LiO2-coder/Smart-home-environment-monitoring-clock/images/2.png

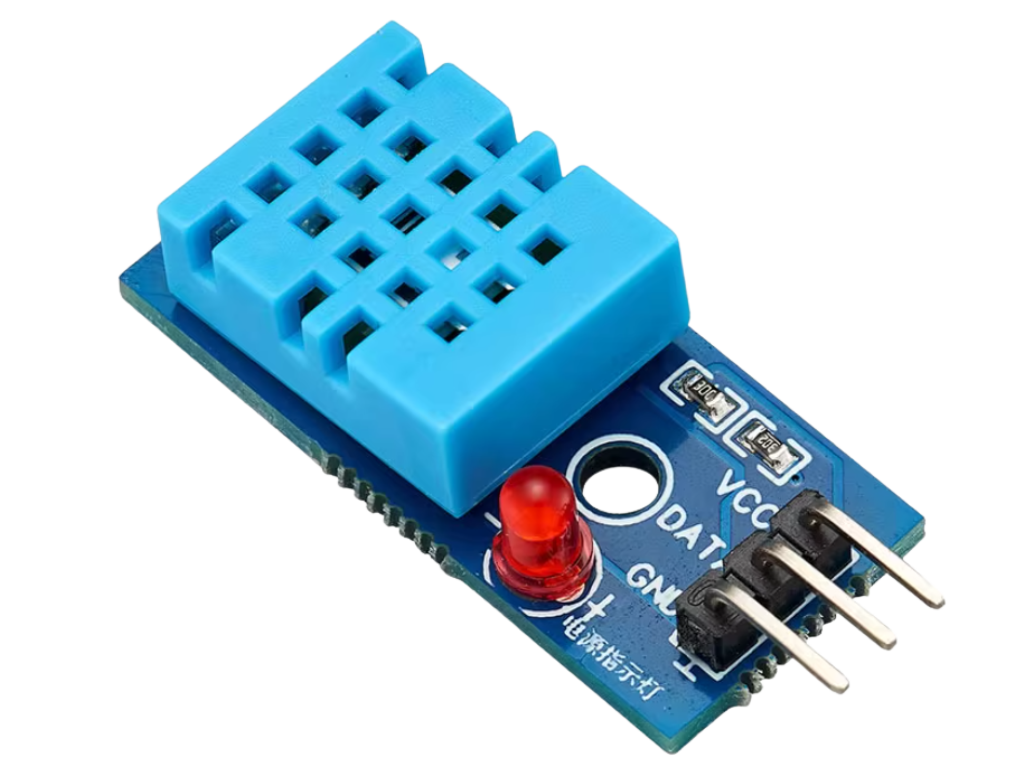
images/2.png
