LiO2-coder/Smart-home-environment-monitoring-clock/images/3.png

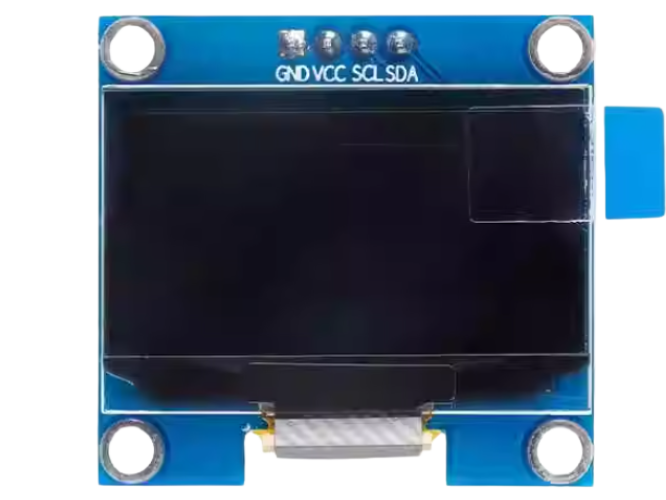
images/3.png
