LiO2-coder/Smart-home-environment-monitoring-clock/images/5.png

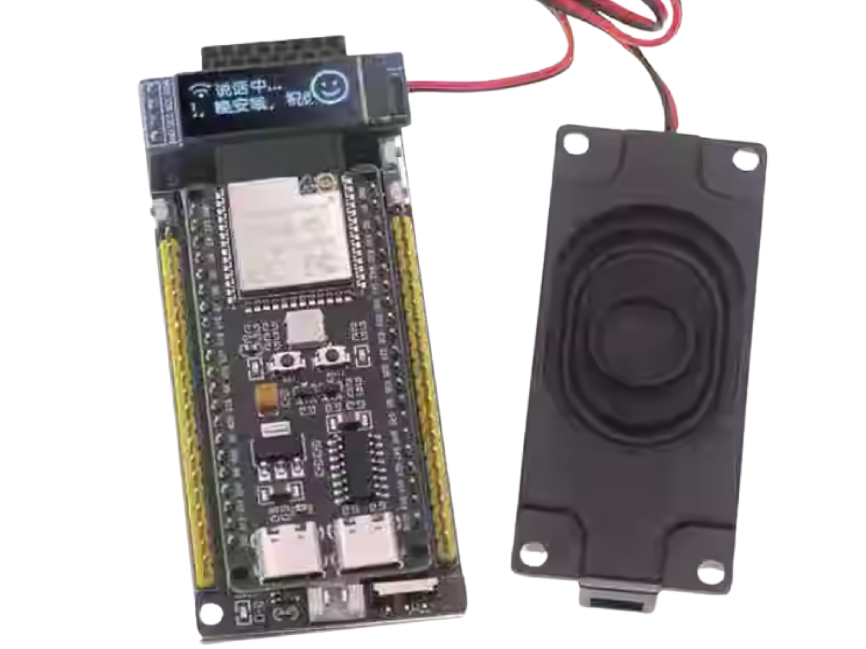
images/5.png
