LiO2-coder/Smart-home-environment-monitoring-clock/images/6.png

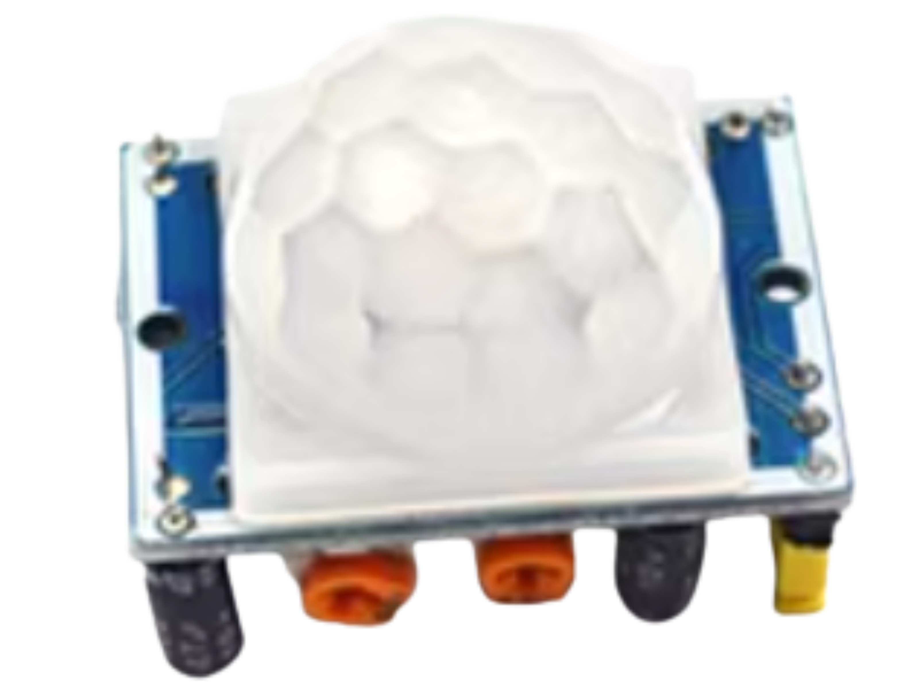
images/6.png
