LiO2-coder/Smart-home-environment-monitoring-clock/images/7.png

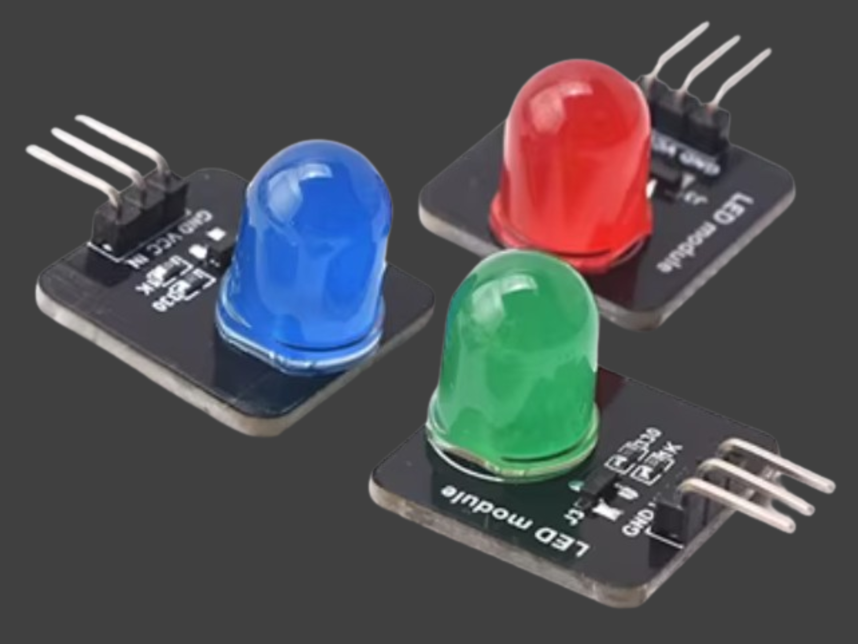
images/7.png
