LiO2-coder/Smart-home-environment-monitoring-clock/images/Alarm/2.2-Alarm-1.png

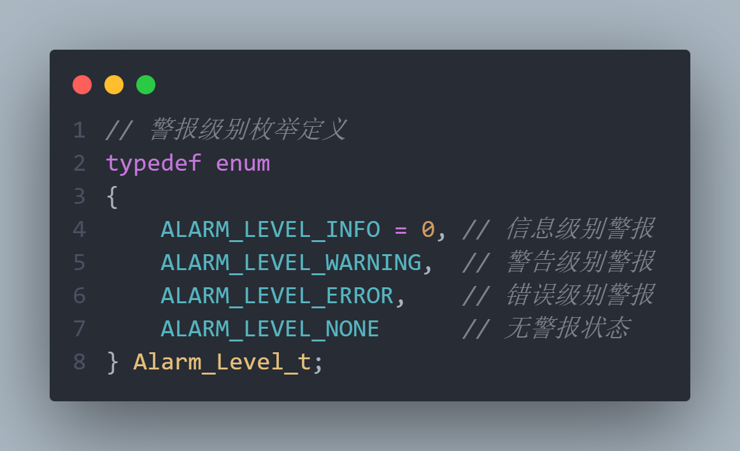
images/Alarm/2.2-Alarm-1.png
