LiO2-coder/Smart-home-environment-monitoring-clock/images/Alarm/2.2-Alarm-5.png

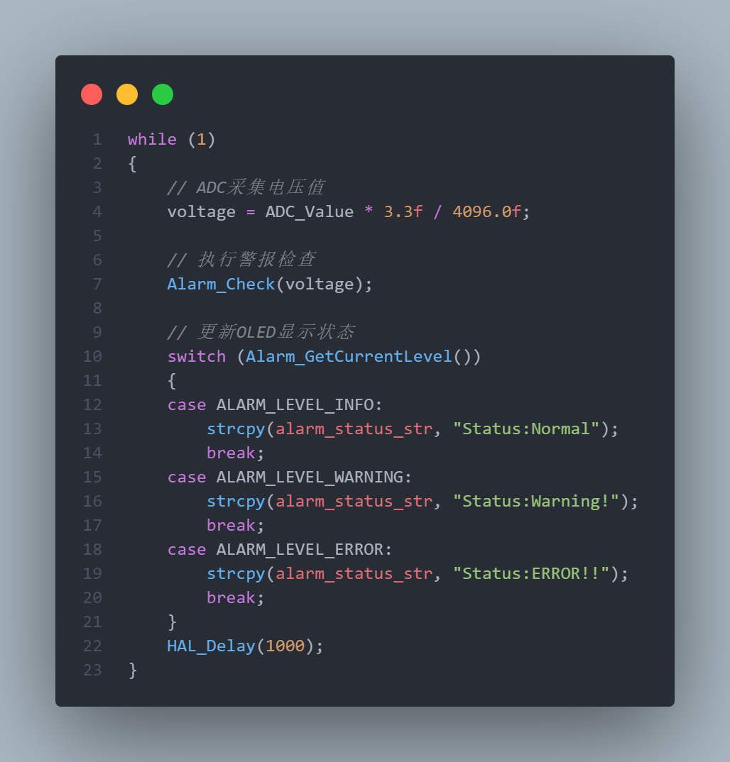
images/Alarm/2.2-Alarm-5.png
