LiO2-coder/Smart-home-environment-monitoring-clock/images/DHT11/2.3-DHT11-2.png

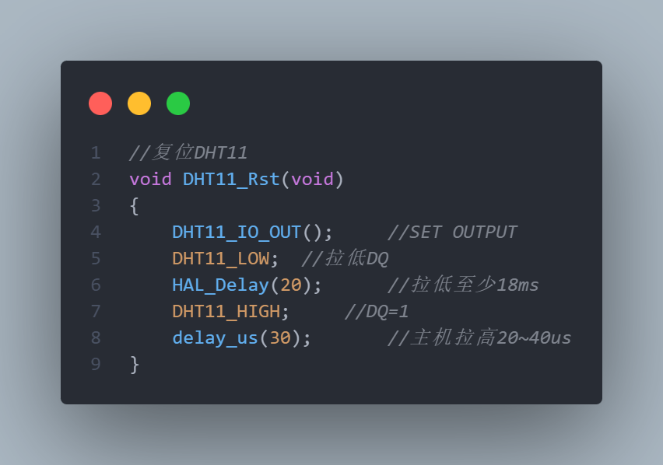
images/DHT11/2.3-DHT11-2.png
