LiO2-coder/Smart-home-environment-monitoring-clock/images/keil5.png

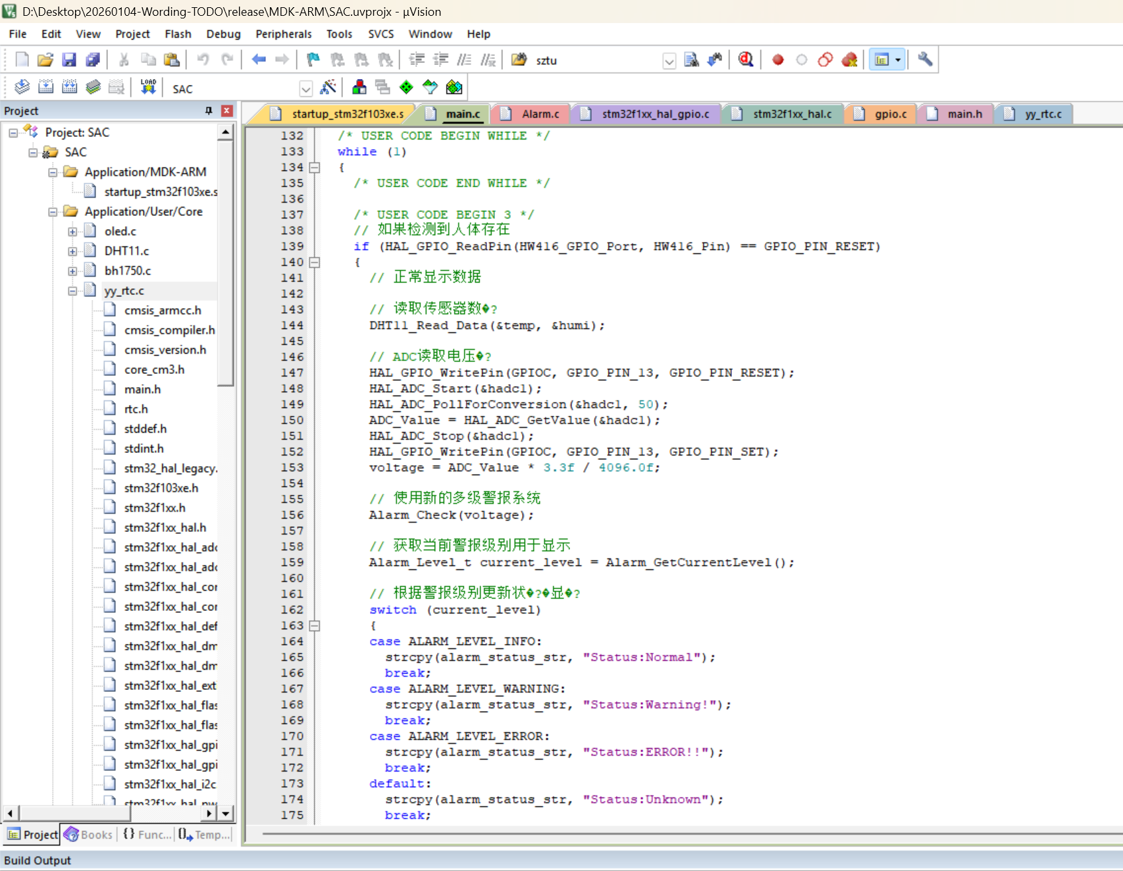
images/keil5.png
