LiO2-coder/Smart-home-environment-monitoring-clock/images/Low Power/2.6-LP-1.png

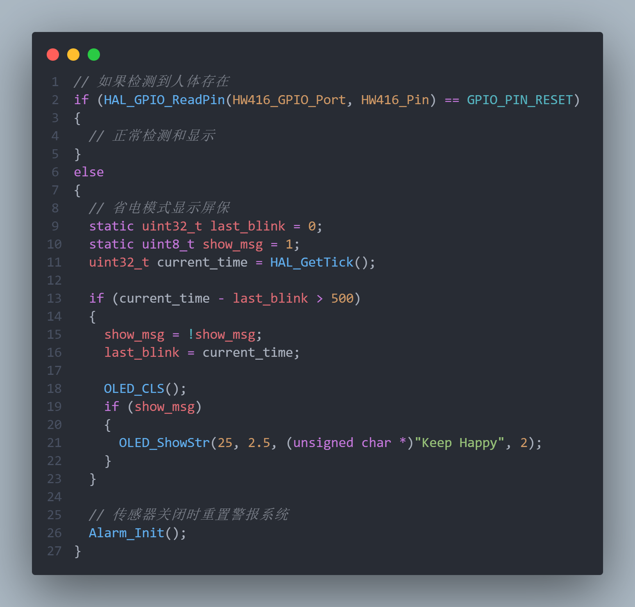
images/Low Power/2.6-LP-1.png
