LiO2-coder/Smart-home-environment-monitoring-clock/images/MQ2/2.1-ADC-1.png

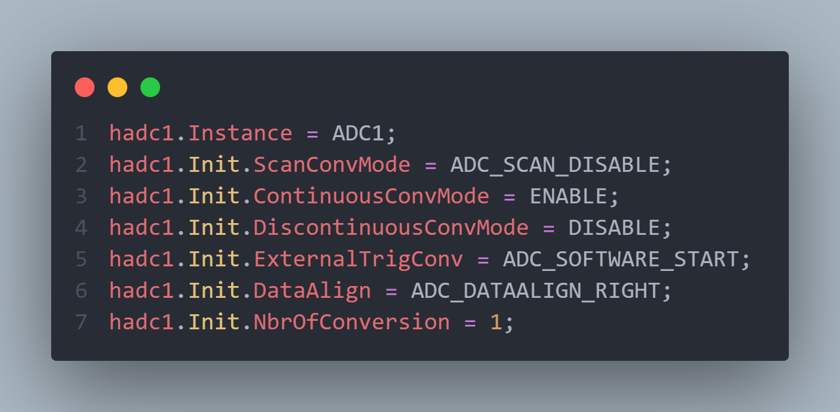
images/MQ2/2.1-ADC-1.png
