LiO2-coder/Smart-home-environment-monitoring-clock/images/MQ2/2.1-ADC-2.png

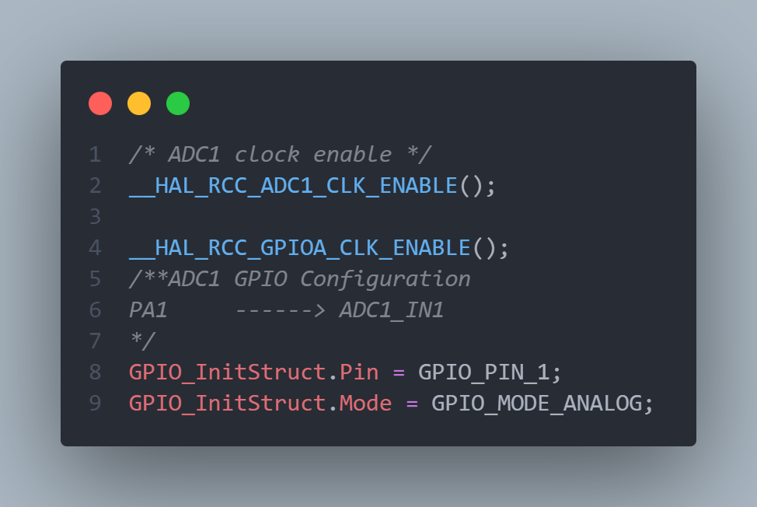
images/MQ2/2.1-ADC-2.png
