LiO2-coder/Smart-home-environment-monitoring-clock/images/MQ2/4.png

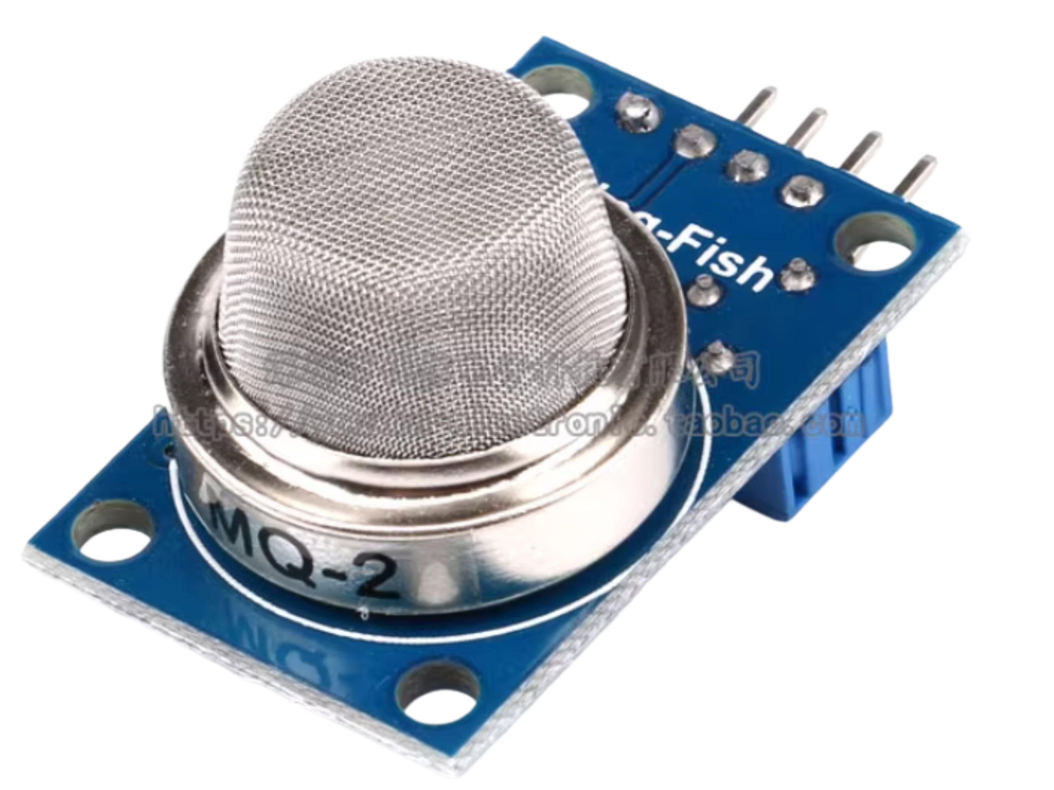
images/MQ2/4.png
