LiO2-coder/Smart-home-environment-monitoring-clock/images/OLED/2.4-oled-3.png

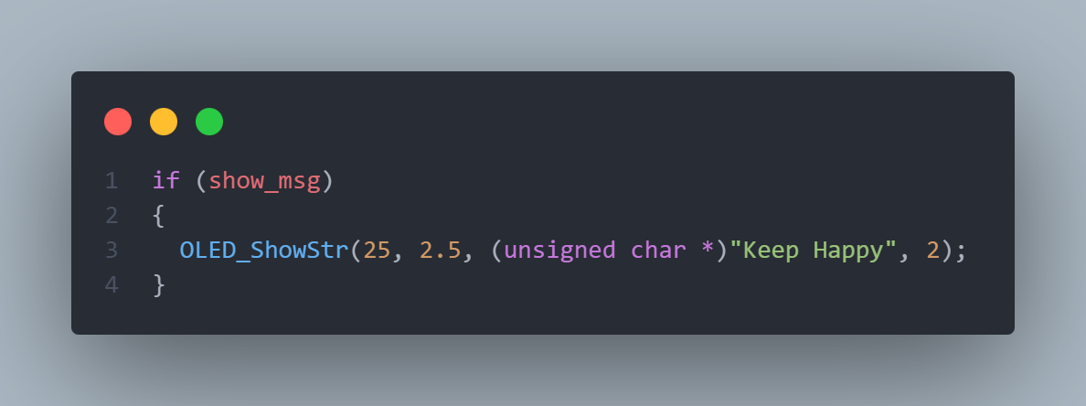
images/OLED/2.4-oled-3.png
