LiO2-coder/Smart-home-environment-monitoring-clock/images/OLED/主界面.jpg

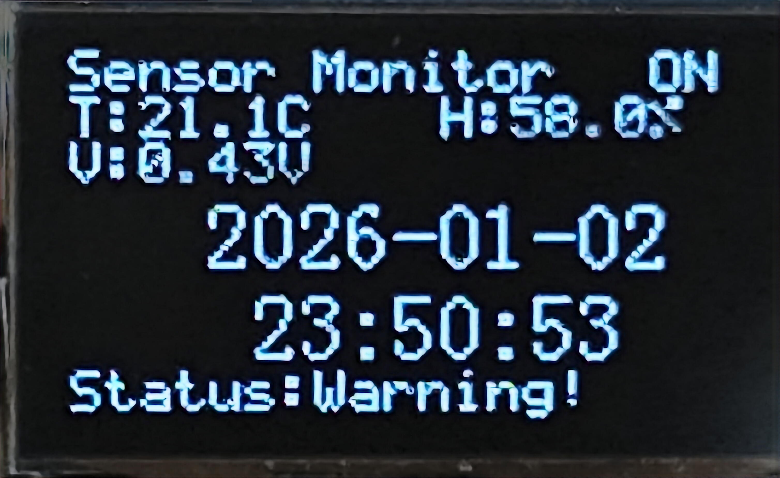
images/OLED/主界面.jpg
