LiO2-coder/Smart-home-environment-monitoring-clock/images/OLED/低功耗显示界面.jpg

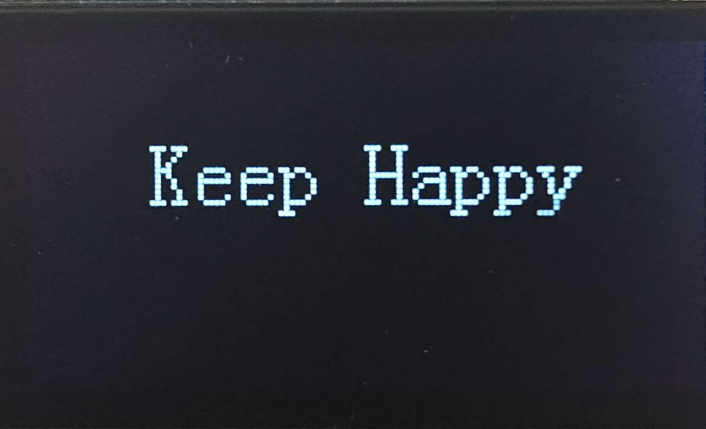
images/OLED/低功耗显示界面.jpg
