LiO2-coder/Smart-home-environment-monitoring-clock/images/OLED/初始化界面.jpg

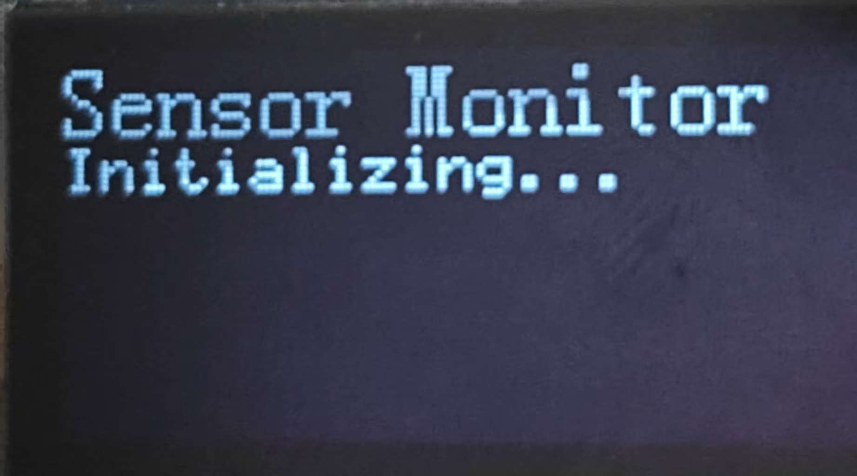
images/OLED/初始化界面.jpg
