LiO2-coder/Smart-home-environment-monitoring-clock/images/rtc/2.5-rtc-1.png

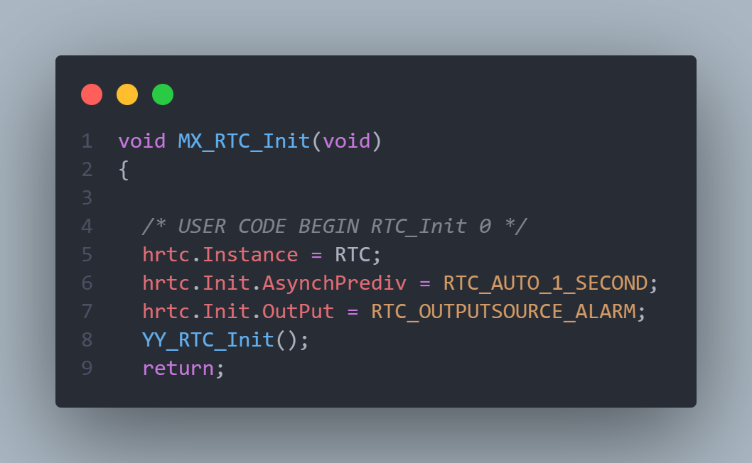
images/rtc/2.5-rtc-1.png
