LiO2-coder/Smart-home-environment-monitoring-clock/images/rtc/2.5-rtc-2.png

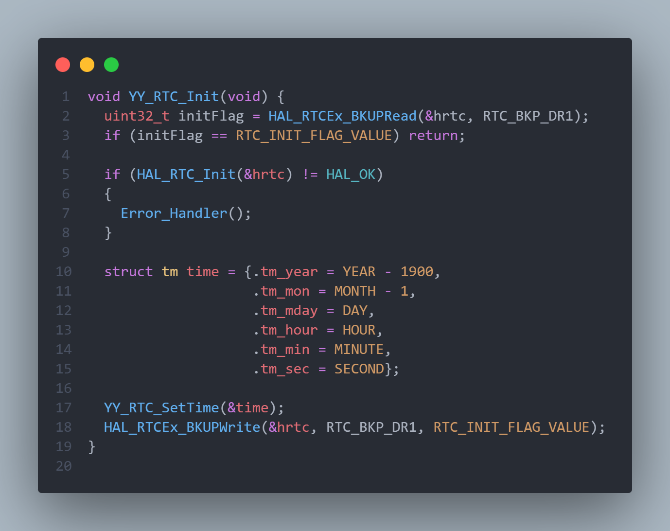
images/rtc/2.5-rtc-2.png
