LiO2-coder/Smart-home-environment-monitoring-clock/images/USART/1.png

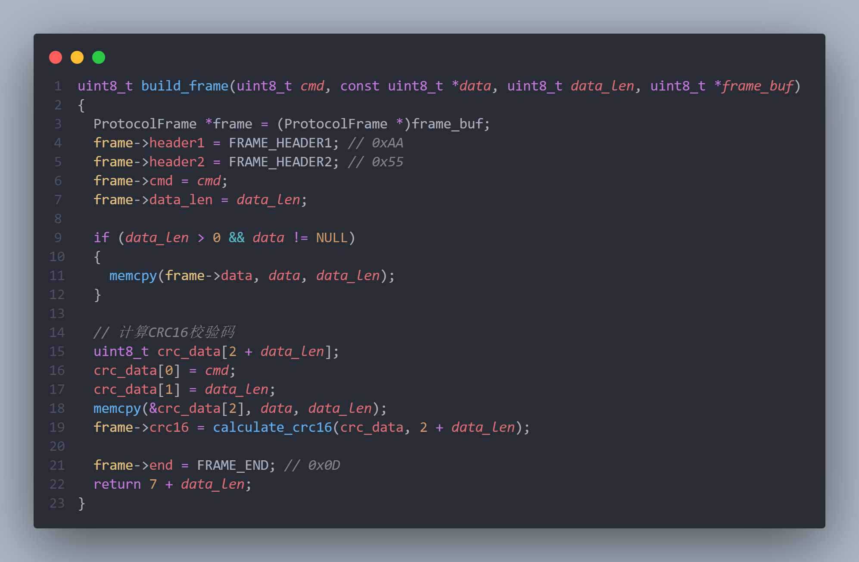
images/USART/1.png
