LiO2-coder/Smart-home-environment-monitoring-clock/images/USART/2.png

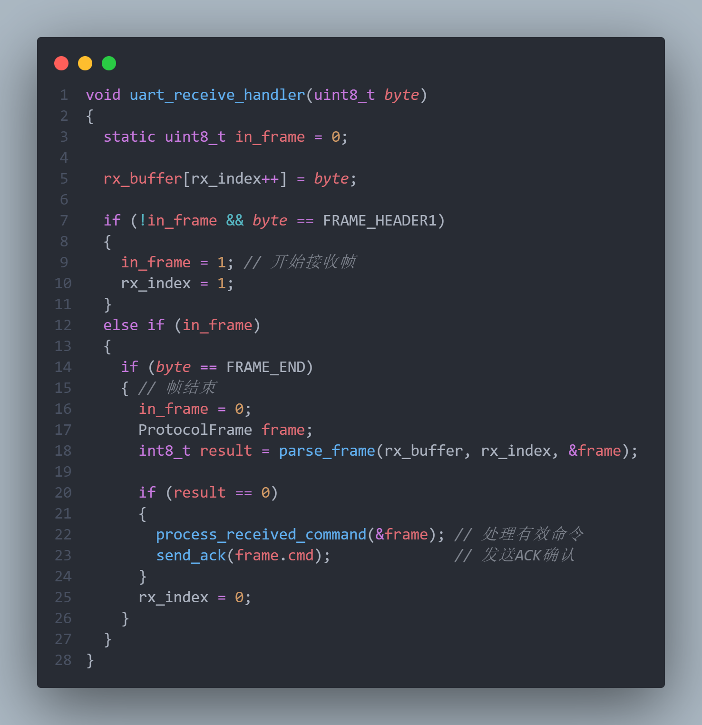
images/USART/2.png
