LiO2-coder/Smart-home-environment-monitoring-clock/images/USART/3.png

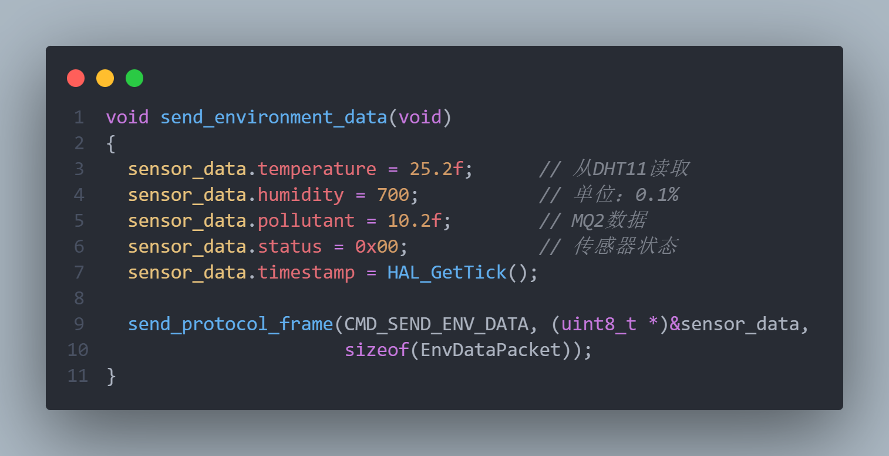
images/USART/3.png
