LiO2-coder/Smart-home-environment-monitoring-clock/images/USART/4.png

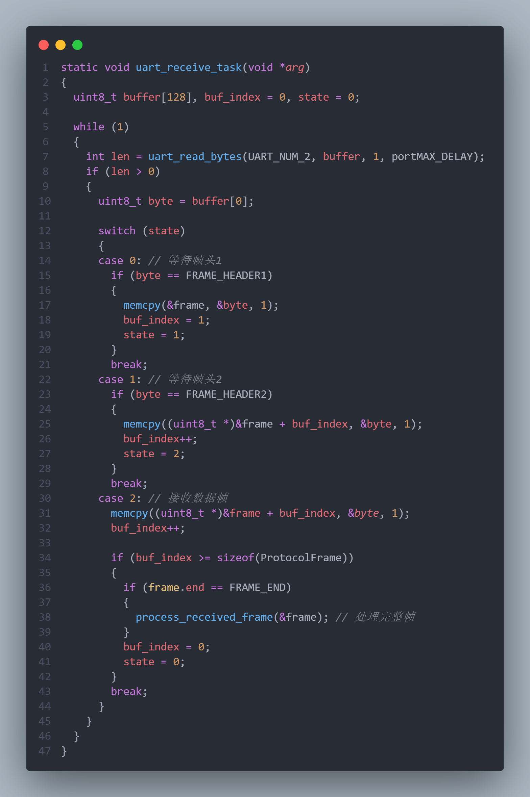
images/USART/4.png
