LiO2-coder/Smart-home-environment-monitoring-clock/images/USART/5.png

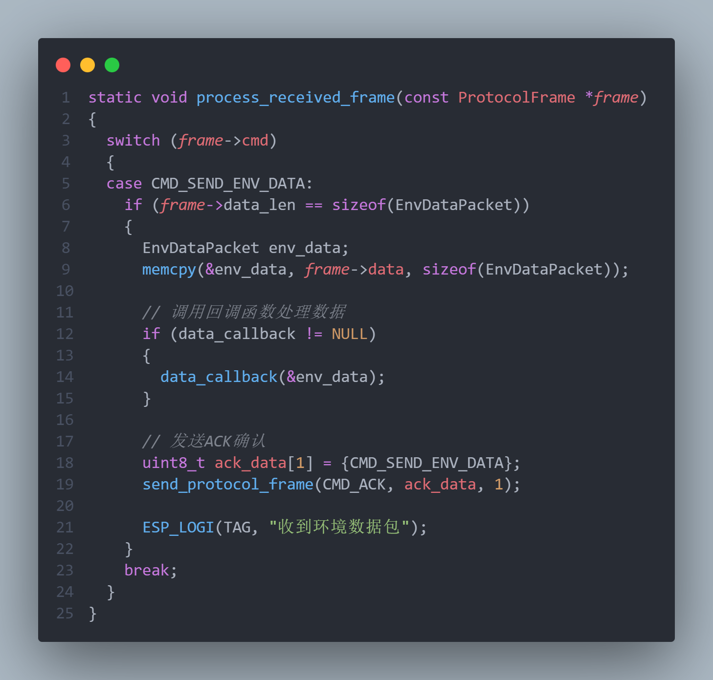
images/USART/5.png
