LiO2-coder/Smart-home-environment-monitoring-clock/images/vscode.png

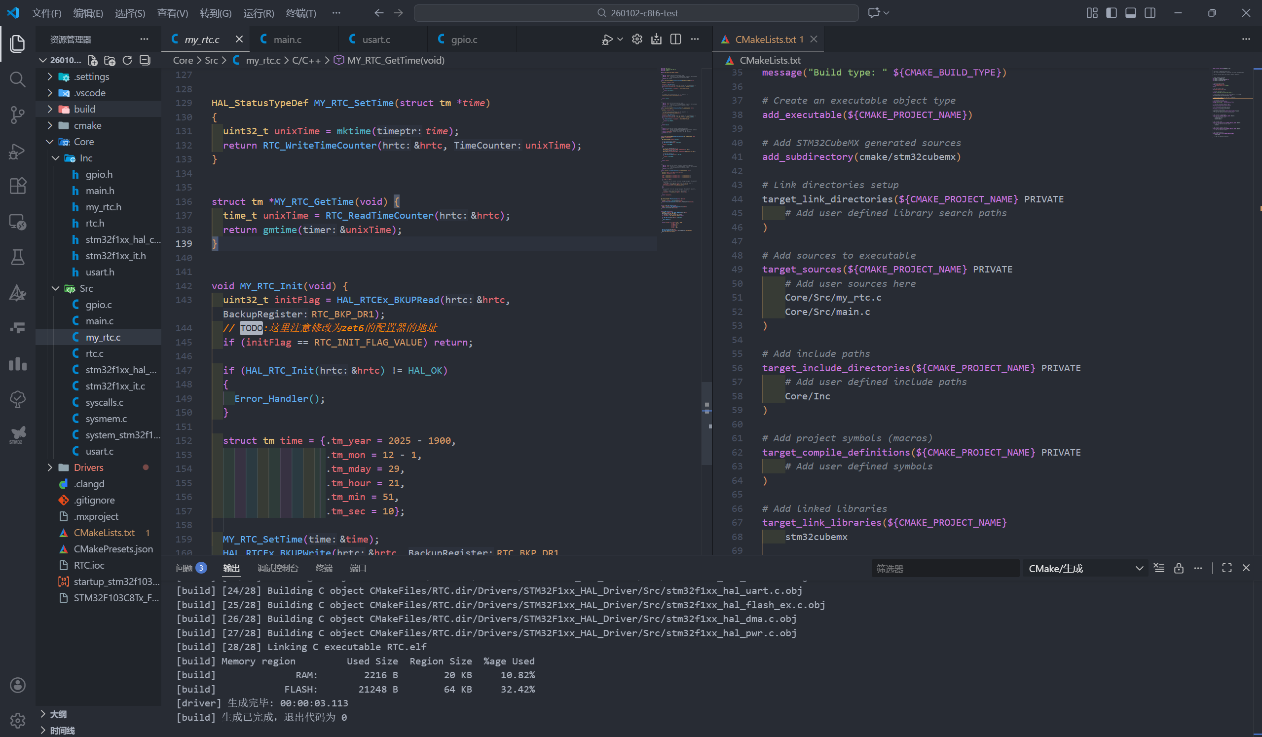
images/vscode.png
