LiO2-coder/Smart-home-environment-monitoring-clock/images/外壳建模1.png

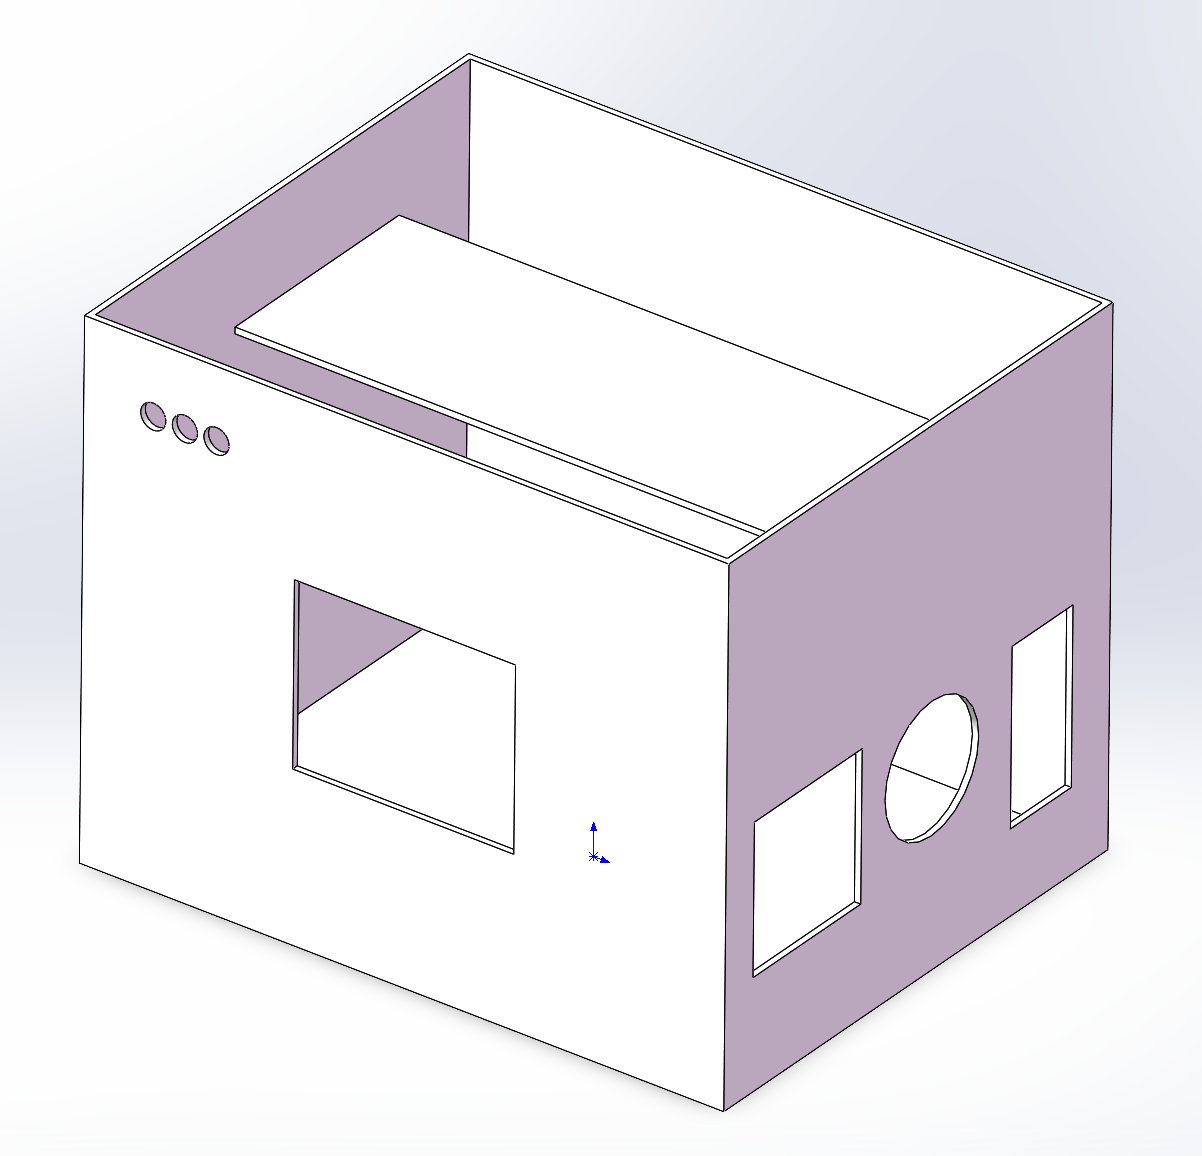
images/外壳建模1.png
