LiO2-coder/Smart-home-environment-monitoring-clock/images/外壳建模2.png

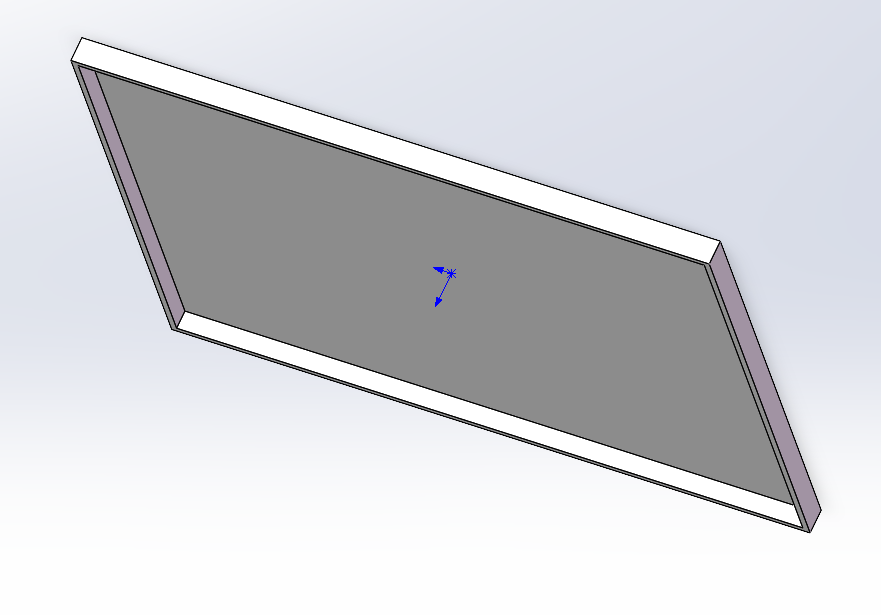
images/外壳建模2.png
