LiO2-coder/Smart-home-environment-monitoring-clock/images/引脚图.png

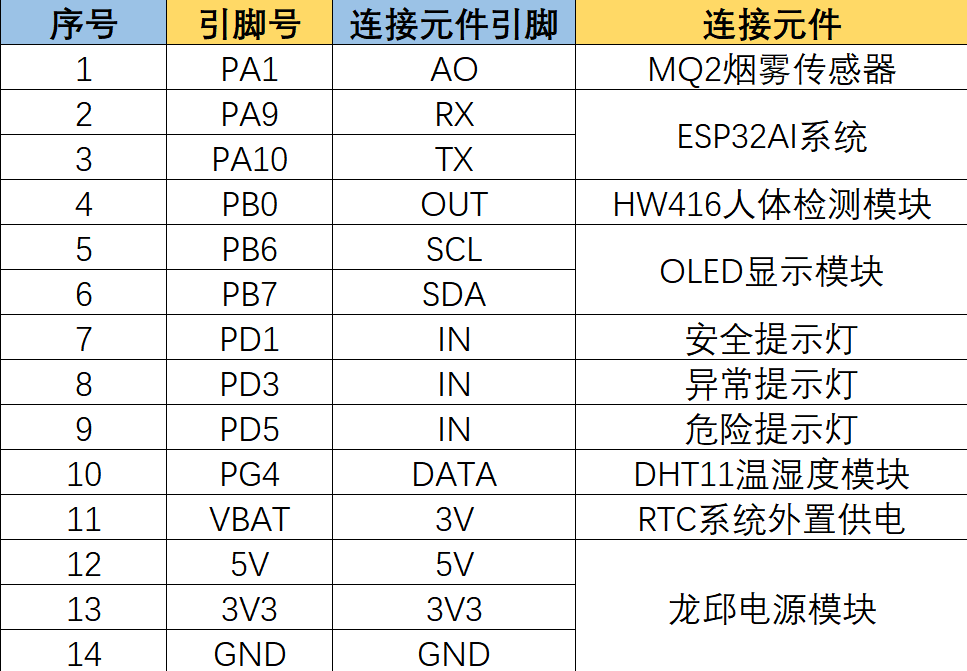
images/引脚图.png
