LiO2-coder/Smart-home-environment-monitoring-clock/images/思维导图.png

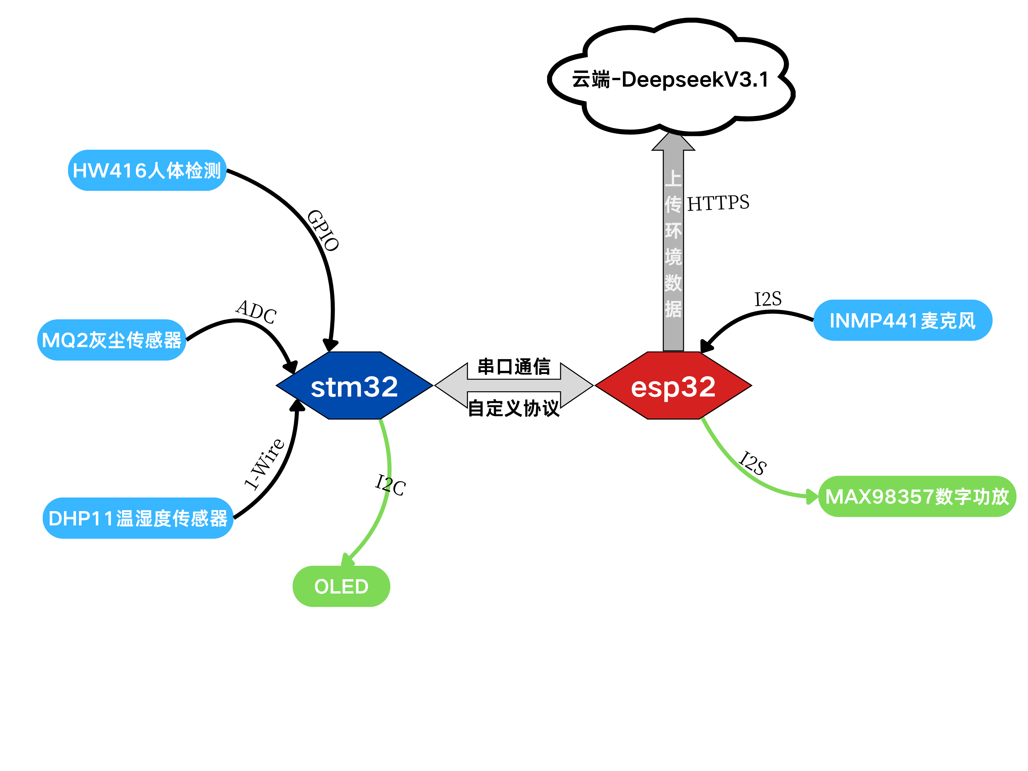
images/思维导图.png
