LiO2-coder/Smart-home-environment-monitoring-clock/images/杜邦线接线.jpg

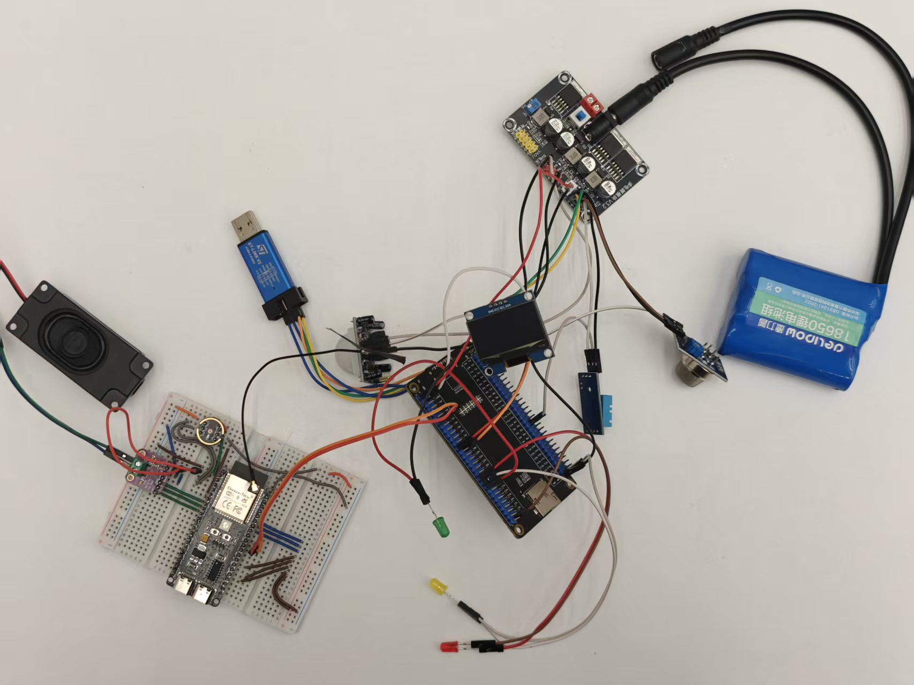
images/杜邦线接线.jpg
