LiO2-coder/Smart-home-environment-monitoring-clock/images/电源模块.png

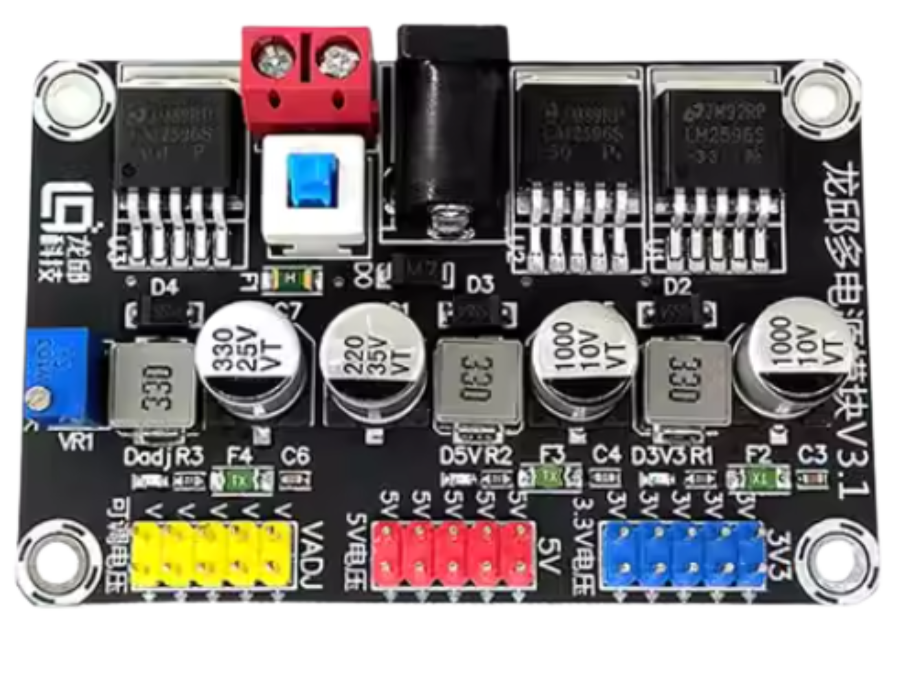
images/电源模块.png
