LiO2-coder/Smart-home-environment-monitoring-clock/images/硬件图.png

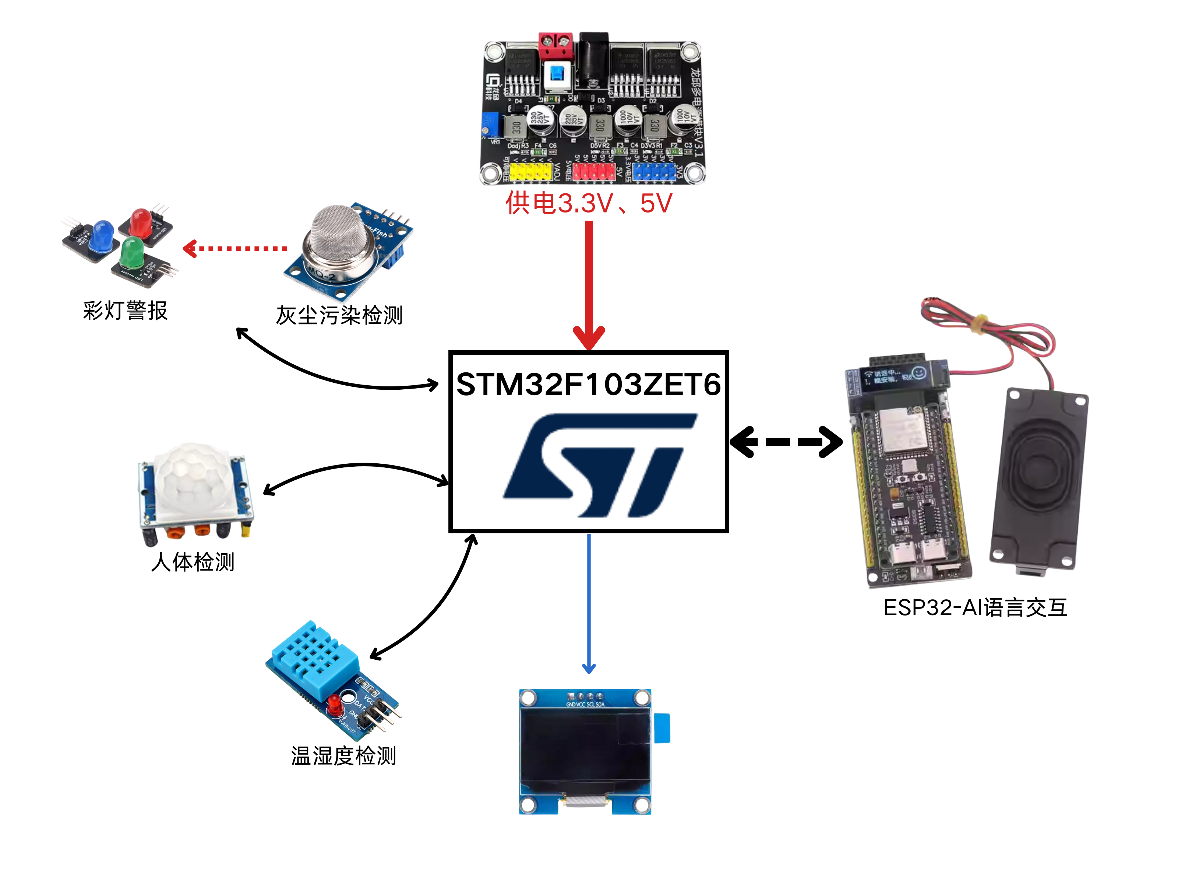
images/硬件图.png
