LiO2-coder/Smart-home-environment-monitoring-clock/images/软件流程图.png

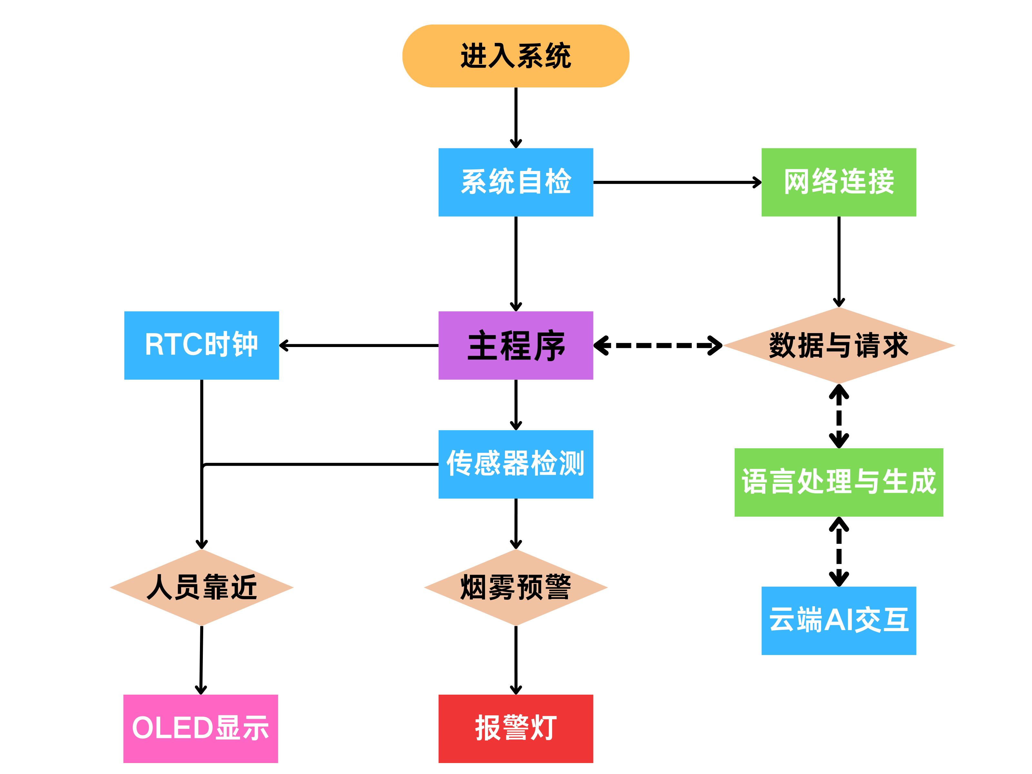
images/软件流程图.png
