LiO2-coder/Smart-home-environment-monitoring-clock/Core/Inc/asc.h

/**
 ***************************************(C) COPYRIGHT 2019 DJI***************************************
 * @file       oledfont.h
 * @brief      character lib of oled
 * @note
 * @Version    V1.0.0
 * @Date       Oct-7-2019      
 ***************************************(C) COPYRIGHT 2019 DJI***************************************
 */
#ifndef __ASCII_H
#define __ASCII_H	 


/***************************16*16?????????:???????????*********/

	unsigned char F16x16[] =
{
0x10,0x60,0x02,0x8C,0x00,0xFE,0x92,0x92,0x92,0x92,0x92,0x92,0x92,0xFE,0x00,0x00,
0x04,0x04,0x7E,0x01,0x00,0xFE,0x88,0x48,0x48,0x00,0x7E,0x90,0x88,0x88,0xE4,0x00,/*"?",0*/

0x80,0x40,0x20,0x90,0x88,0x86,0x80,0x80,0x80,0x83,0x8C,0x10,0x20,0x40,0x80,0x00,
0x00,0x80,0x40,0x20,0x18,0x07,0x00,0x40,0x80,0x40,0x3F,0x00,0x00,0x00,0x00,0x00,/*"?",1*/

0x00,0x00,0xFE,0x22,0x22,0x22,0x22,0x22,0x22,0x22,0x22,0xE2,0x02,0x00,0x00,0x00,
0x00,0x00,0x7F,0x42,0x42,0x42,0x42,0x42,0x42,0x42,0x42,0x43,0x40,0x40,0x00,0x00,/*"?",2*/
	
0x00,0x00,0x7C,0x54,0x55,0x56,0x54,0x7C,0x54,0x56,0x55,0x54,0x7C,0x00,0x00,0x00,
0x01,0x01,0x01,0xFD,0x45,0x45,0x45,0x45,0x45,0x45,0x45,0xFD,0x01,0x01,0x01,0x00,/*"?",3*/

0x10,0x10,0x10,0x10,0x10,0xFF,0x10,0x10,0xF0,0x10,0x11,0x16,0xD0,0x10,0x10,0x00,
0x80,0x40,0x20,0x18,0x06,0x41,0x20,0x10,0x3F,0x44,0x42,0x41,0x40,0x40,0x78,0x00,/*"?",4*/

0x04,0x04,0x04,0x04,0xFF,0x24,0x24,0x24,0x24,0x24,0xFF,0x04,0x04,0x04,0x04,0x00,
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
  0x08,0xF8,0x88,0x88,0xE8,0x08,0x10,0x00,0x20,0x3F,0x20,0x20,0x23,0x20,0x18,0x00,//E 37
  0x08,0xF8,0x88,0x88,0xE8,0x08,0x10,0x00,0x20,0x3F,0x20,0x00,0x03,0x00,0x00,0x00,//F 38
  0xC0,0x30,0x08,0x08,0x08,0x38,0x00,0x00,0x07,0x18,0x20,0x20,0x22,0x1E,0x02,0x00,//G 39
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
};

#endif
