LiO2-coder/Smart-home-environment-monitoring-clock/Core/Src/yy_rtc.c

#include "yy_rtc.h"
#include "stm32f1xx_hal_def.h"
#include <time.h>

#define RTC_INIT_FLAG_VALUE 0x02333

#define YEAR 2026
#define MONTH 1
#define DAY 2

#define HOUR 23
#define MINUTE 50
#define SECOND 0

/**
  * @brief  Enters the RTC Initialization mode.
  * @param  hrtc   pointer to a RTC_HandleTypeDef structure that contains
  *                the configuration information for RTC.
  * @retval HAL status
  */
static HAL_StatusTypeDef RTC_EnterInitMode(RTC_HandleTypeDef *hrtc)
{
  uint32_t tickstart = 0U;

  tickstart = HAL_GetTick();
  /* Wait till RTC is in INIT state and if Time out is reached exit */
  while ((hrtc->Instance->CRL & RTC_CRL_RTOFF) == (uint32_t)RESET)
  {
    if ((HAL_GetTick() - tickstart) >  RTC_TIMEOUT_VALUE)
    {
      return HAL_TIMEOUT;
    }
  }

  /* Disable the write protection for RTC registers */
  __HAL_RTC_WRITEPROTECTION_DISABLE(hrtc);


  return HAL_OK;
}


/**
  * @brief  Exit the RTC Initialization mode.
  * @param  hrtc   pointer to a RTC_HandleTypeDef structure that contains
  *                the configuration information for RTC.
  * @retval HAL status
  */
static HAL_StatusTypeDef RTC_ExitInitMode(RTC_HandleTypeDef *hrtc)
{
  uint32_t tickstart = 0U;

  /* Disable the write protection for RTC registers */
  __HAL_RTC_WRITEPROTECTION_ENABLE(hrtc);

  tickstart = HAL_GetTick();
  /* Wait till RTC is in INIT state and if Time out is reached exit */
  while ((hrtc->Instance->CRL & RTC_CRL_RTOFF) == (uint32_t)RESET)
  {
    if ((HAL_GetTick() - tickstart) >  RTC_TIMEOUT_VALUE)
    {
      return HAL_TIMEOUT;
    }
  }

  return HAL_OK;
}

/**
 * @brief  Write the time counter in RTC_CNT registers.
 * @param  hrtc   pointer to a RTC_HandleTypeDef structure that contains
 *                the configuration information for RTC.
 * @param  TimeCounter: Counter to write in RTC_CNT registers
 * @retval HAL status
 */


static HAL_StatusTypeDef RTC_WriteTimeCounter(RTC_HandleTypeDef *hrtc, uint32_t TimeCounter)
{
  HAL_StatusTypeDef status = HAL_OK;

  /* Set Initialization mode */
  if (RTC_EnterInitMode(hrtc) != HAL_OK)
  {
    status = HAL_ERROR;
  }
  else
  {
    /* Set RTC COUNTER MSB word */
    WRITE_REG(hrtc->Instance->CNTH, (TimeCounter >> 16U));
    /* Set RTC COUNTER LSB word */
    WRITE_REG(hrtc->Instance->CNTL, (TimeCounter & RTC_CNTL_RTC_CNT));

    /* Wait for synchro */
    if (RTC_ExitInitMode(hrtc) != HAL_OK)
    {
      status = HAL_ERROR;
    }
  }

  return status;
}


/**
  * @brief  Read the time counter available in RTC_CNT registers.
  * @param  hrtc   pointer to a RTC_HandleTypeDef structure that contains
  *                the configuration information for RTC.
  * @retval Time counter
  */
static uint32_t RTC_ReadTimeCounter(RTC_HandleTypeDef *hrtc)
{
  uint16_t high1 = 0U, high2 = 0U, low = 0U;
  uint32_t timecounter = 0U;

  high1 = READ_REG(hrtc->Instance->CNTH & RTC_CNTH_RTC_CNT);
  low   = READ_REG(hrtc->Instance->CNTL & RTC_CNTL_RTC_CNT);
  high2 = READ_REG(hrtc->Instance->CNTH & RTC_CNTH_RTC_CNT);

  if (high1 != high2)
  {
    /* In this case the counter roll over during reading of CNTL and CNTH registers,
       read again CNTL register then return the counter value */
    timecounter = (((uint32_t) high2 << 16U) | READ_REG(hrtc->Instance->CNTL & RTC_CNTL_RTC_CNT));
  }
  else
  {
    /* No counter roll over during reading of CNTL and CNTH registers, counter
       value is equal to first value of CNTL and CNTH */
    timecounter = (((uint32_t) high1 << 16U) | low);
  }

  return timecounter;
}


HAL_StatusTypeDef YY_RTC_SetTime(struct tm *time)
{
  uint32_t unixTime = mktime(time);
  return RTC_WriteTimeCounter(&hrtc, unixTime);
}


struct tm *YY_RTC_GetTime(void) {
    static struct tm timeinfo;  // 使用静态变量避免返回局部变量地址
    time_t unixTime = RTC_ReadTimeCounter(&hrtc);
    
    // 检查时间是否有效
    if (unixTime == 0 || unixTime == 0xFFFFFFFF) {
        return NULL;
    }
    
    // 使用localtime而不是gmtime，因为gmtime返回的是UTC时间
    timeinfo = *localtime(&unixTime);
    return &timeinfo;
}


void YY_RTC_Init(void) {
  uint32_t initFlag = HAL_RTCEx_BKUPRead(&hrtc, RTC_BKP_DR1);
  if (initFlag == RTC_INIT_FLAG_VALUE) return;

  if (HAL_RTC_Init(&hrtc) != HAL_OK)
  {
    Error_Handler();
  }

  struct tm time = {.tm_year = YEAR - 1900,
                    .tm_mon = MONTH - 1,
                    .tm_mday = DAY,
                    .tm_hour = HOUR,
                    .tm_min = MINUTE,
                    .tm_sec = SECOND};

  YY_RTC_SetTime(&time);
  HAL_RTCEx_BKUPWrite(&hrtc, RTC_BKP_DR1, RTC_INIT_FLAG_VALUE);
}
